rguilmet/magnetic-field-scanner/docs/electrical/wiring/RM3100 Breakout Board augumented pinout.png

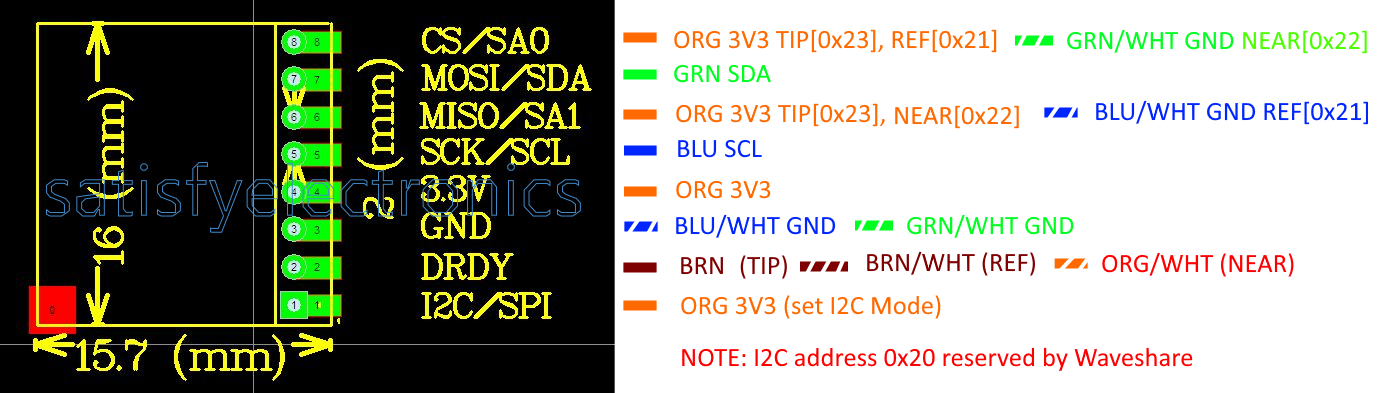
docs/electrical/wiring/RM3100 Breakout Board augumented pinout.png
