rguilmet/magnetic-field-scanner/docs/images/ESP32-S3-Touch-LCD-3.49-ArduinoToolCfg-18487604f20ee06f9c543932301bdffe.png

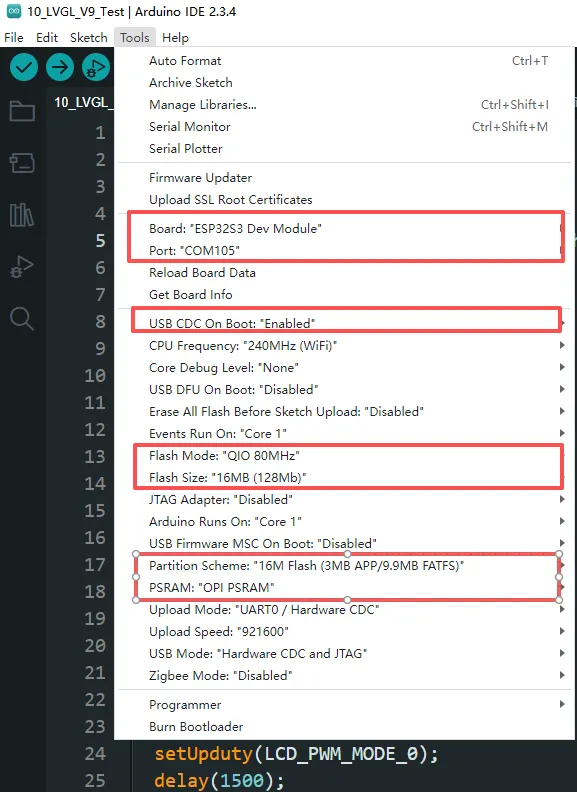
docs/images/ESP32-S3-Touch-LCD-3.49-ArduinoToolCfg-18487604f20ee06f9c543932301bdffe.png
