rguilmet/magnetic-field-scanner/docs/images/ESP32-S3-Touch-LCD-3.49-Blank_Portrait.png

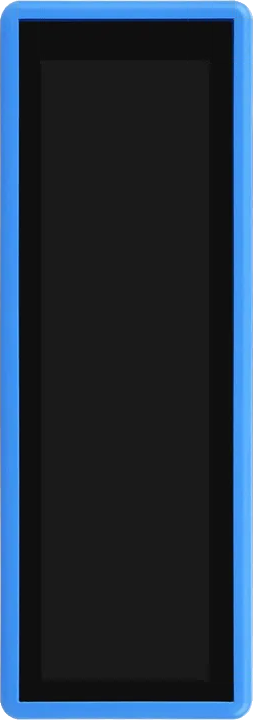
docs/images/ESP32-S3-Touch-LCD-3.49-Blank_Portrait.png
