rguilmet/magnetic-field-scanner/docs/images/ESP32-S3-Touch-LCD-3.49-DocHeader-1-2669fb1ab64cd743be19858549427792.png

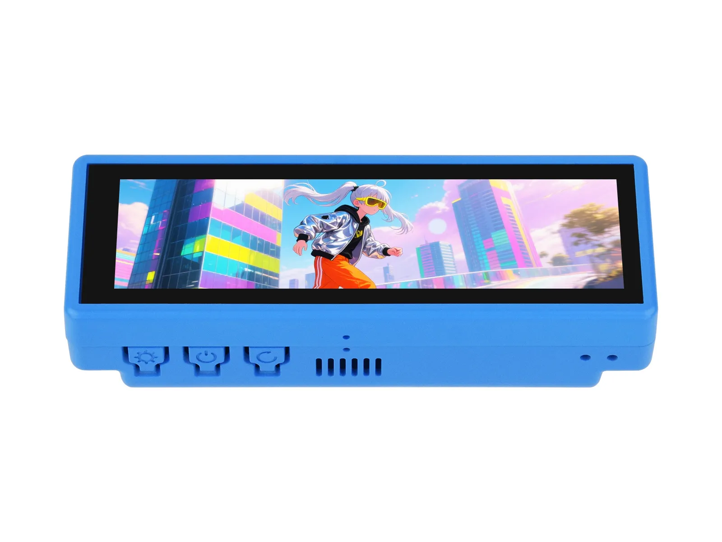
docs/images/ESP32-S3-Touch-LCD-3.49-DocHeader-1-2669fb1ab64cd743be19858549427792.png
