rguilmet/magnetic-field-scanner/docs/images/ESP32-S3-Touch-LCD-3.49-HW-d45f2a0617c5f4e05d497ae3533752b7.png

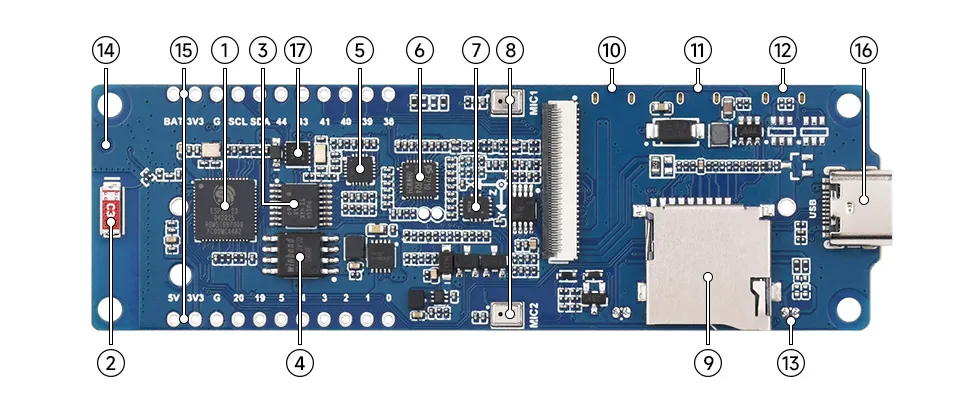
docs/images/ESP32-S3-Touch-LCD-3.49-HW-d45f2a0617c5f4e05d497ae3533752b7.png
