rguilmet/magnetic-field-scanner/docs/images/ESP32-S3-Touch-LCD-3.49-ProductSize-1-b798e9adb46e2dde7847e5227739baf6.png

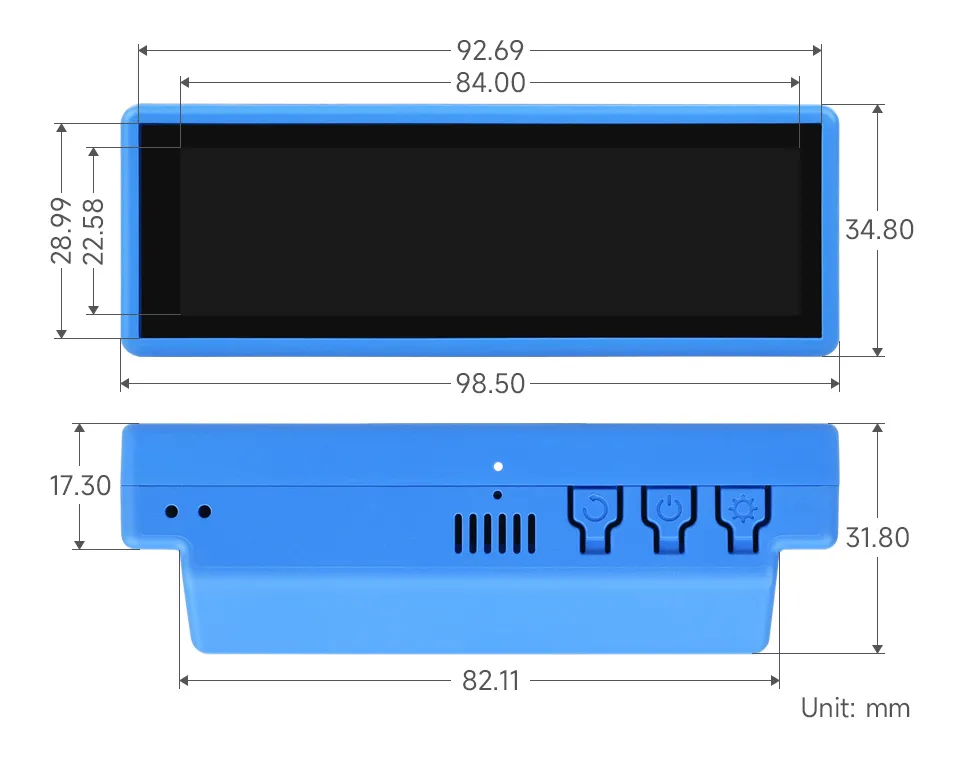
docs/images/ESP32-S3-Touch-LCD-3.49-ProductSize-1-b798e9adb46e2dde7847e5227739baf6.png
