rguilmet/magnetic-field-scanner/docs/images/ESP32-S3-Touch-LCD-3.49-ProductSize-2-53f7565186c1f234cee2f71812a7628d.png

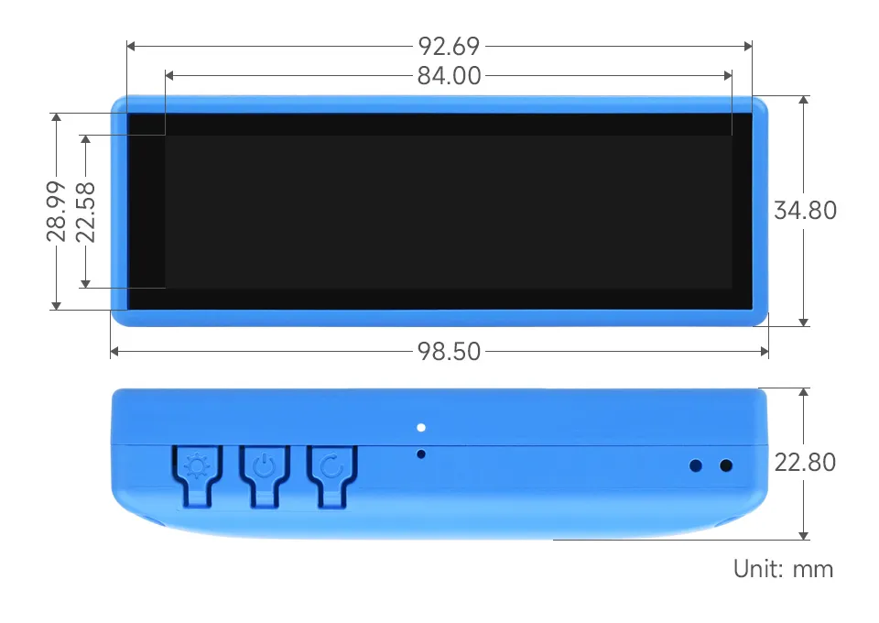
docs/images/ESP32-S3-Touch-LCD-3.49-ProductSize-2-53f7565186c1f234cee2f71812a7628d.png
