rguilmet/magnetic-field-scanner/docs/images/full_res/Magnetic Field Scanner - Exploded View - Closeup REF BACK (20260914_163832).png

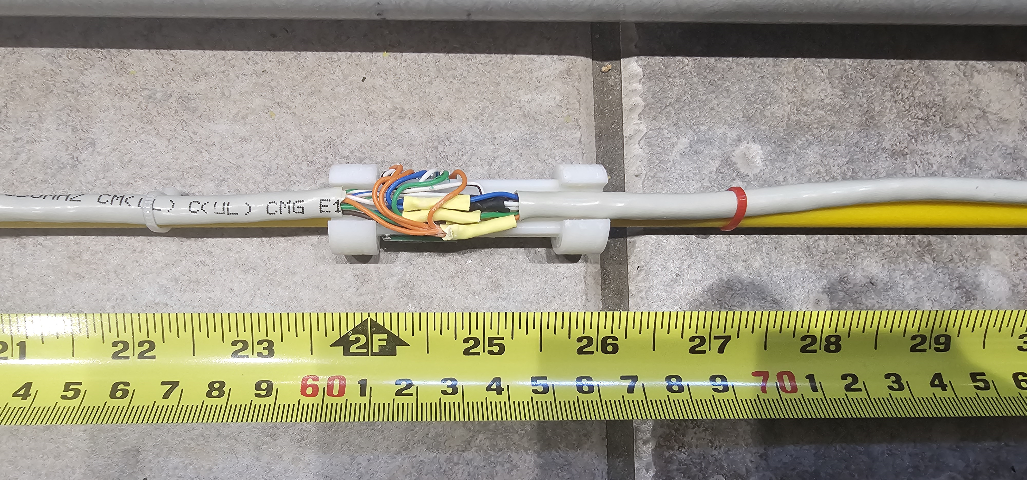
docs/images/full_res/Magnetic Field Scanner - Exploded View - Closeup REF BACK (20260914_163832).png
