rguilmet/magnetic-field-scanner/docs/images/full_res/Magnetic Field Scanner - Exploded View - Closeup TIP BACK (20260914_163811).png

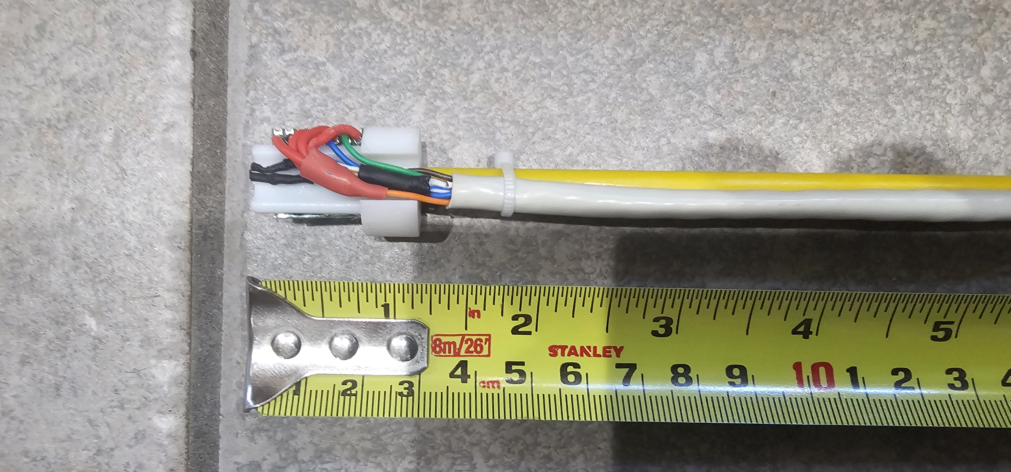
docs/images/full_res/Magnetic Field Scanner - Exploded View - Closeup TIP BACK (20260914_163811).png
