rguilmet/magnetic-field-scanner/docs/images/full_res/Magnetic Field Scanner - Inside Shot Overview (20260914_160351).png

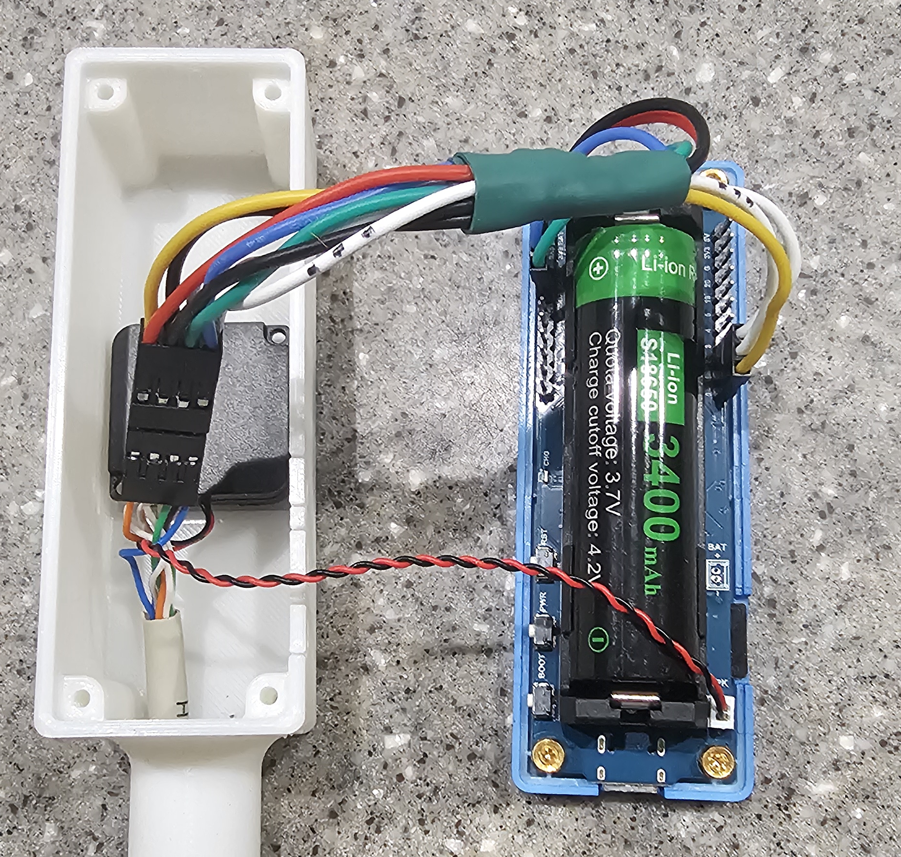
docs/images/full_res/Magnetic Field Scanner - Inside Shot Overview (20260914_160351).png
