rguilmet/magnetic-field-scanner/docs/images/Magnetic Field Scanner - Main Screen - AUTO.png

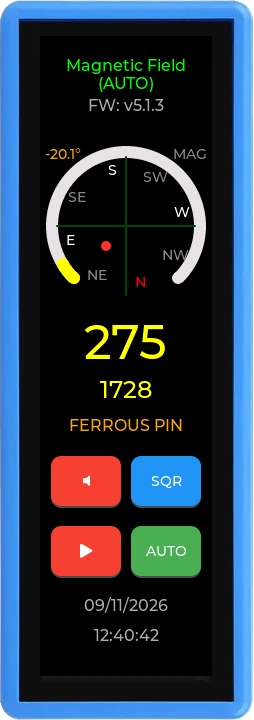
docs/images/Magnetic Field Scanner - Main Screen - AUTO.png
