rguilmet/magnetic-field-scanner/docs/images/Magnetic Field Scanner - Main Screen - RAW.png

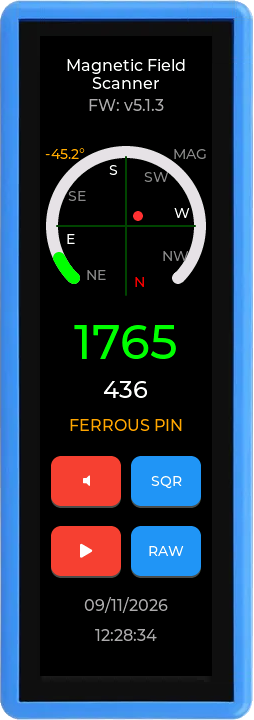
docs/images/Magnetic Field Scanner - Main Screen - RAW.png
