rguilmet/magnetic-field-scanner/docs/images/Magnetic Field Scanner - Mechanical Overview - 3 Sensor.png

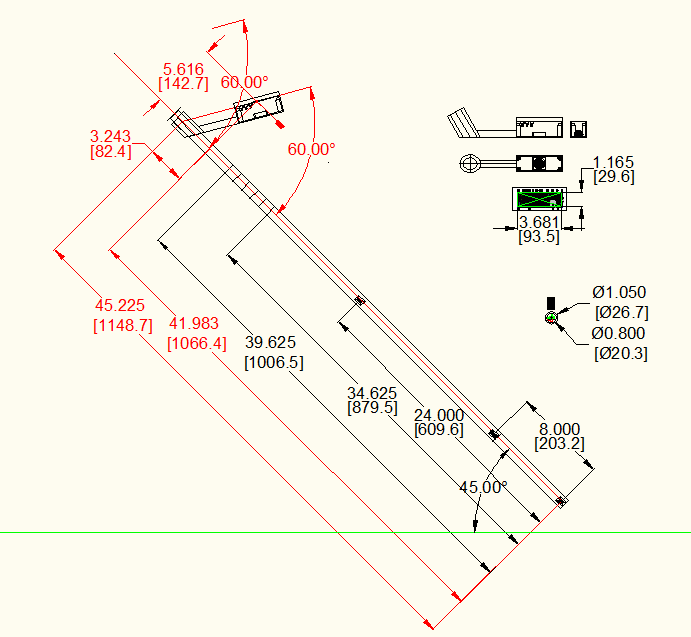
docs/images/Magnetic Field Scanner - Mechanical Overview - 3 Sensor.png
