rguilmet/magnetic-field-scanner/docs/images/Magnetic Field Scanner - Mechanical Overview.png

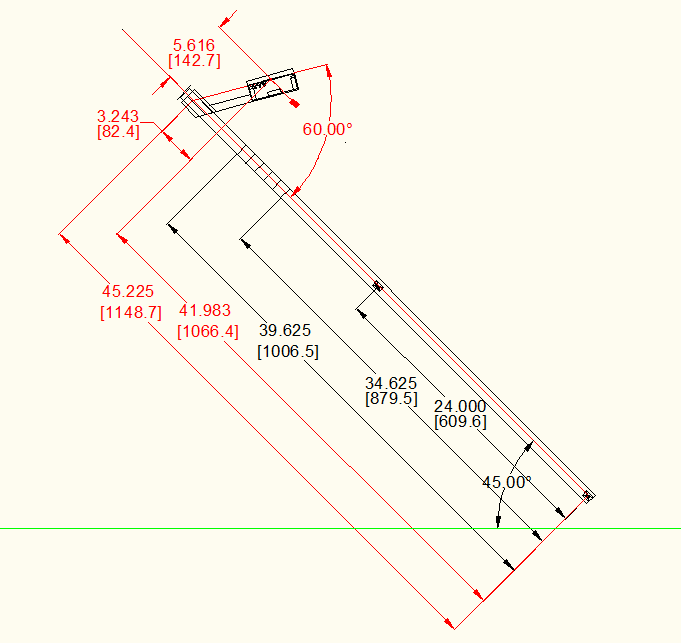
docs/images/Magnetic Field Scanner - Mechanical Overview.png
