rguilmet/magnetic-field-scanner/docs/images/Magnetic Field Scanner - System & Hardware - 200 CC.png

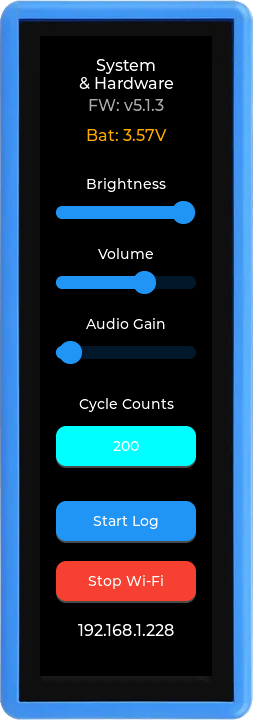
docs/images/Magnetic Field Scanner - System & Hardware - 200 CC.png
