rguilmet/magnetic-field-scanner/docs/reports/plot_45_45_400CC.png

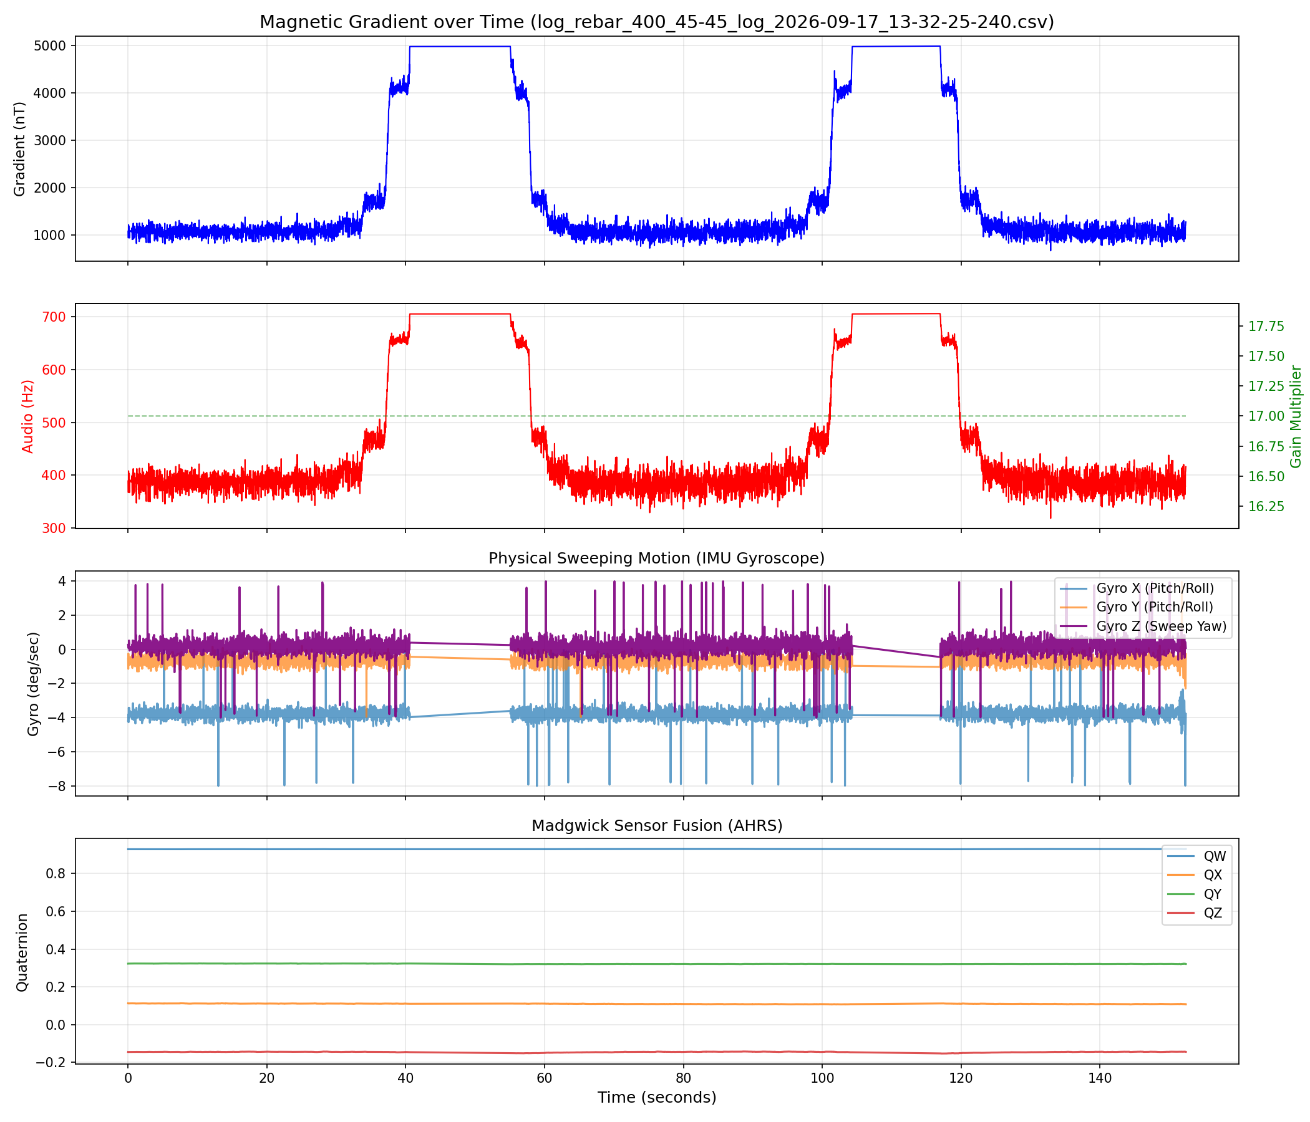
docs/reports/plot_45_45_400CC.png
