rguilmet/magnetic-field-scanner/docs/reports/plot_45_45_3200CC.png

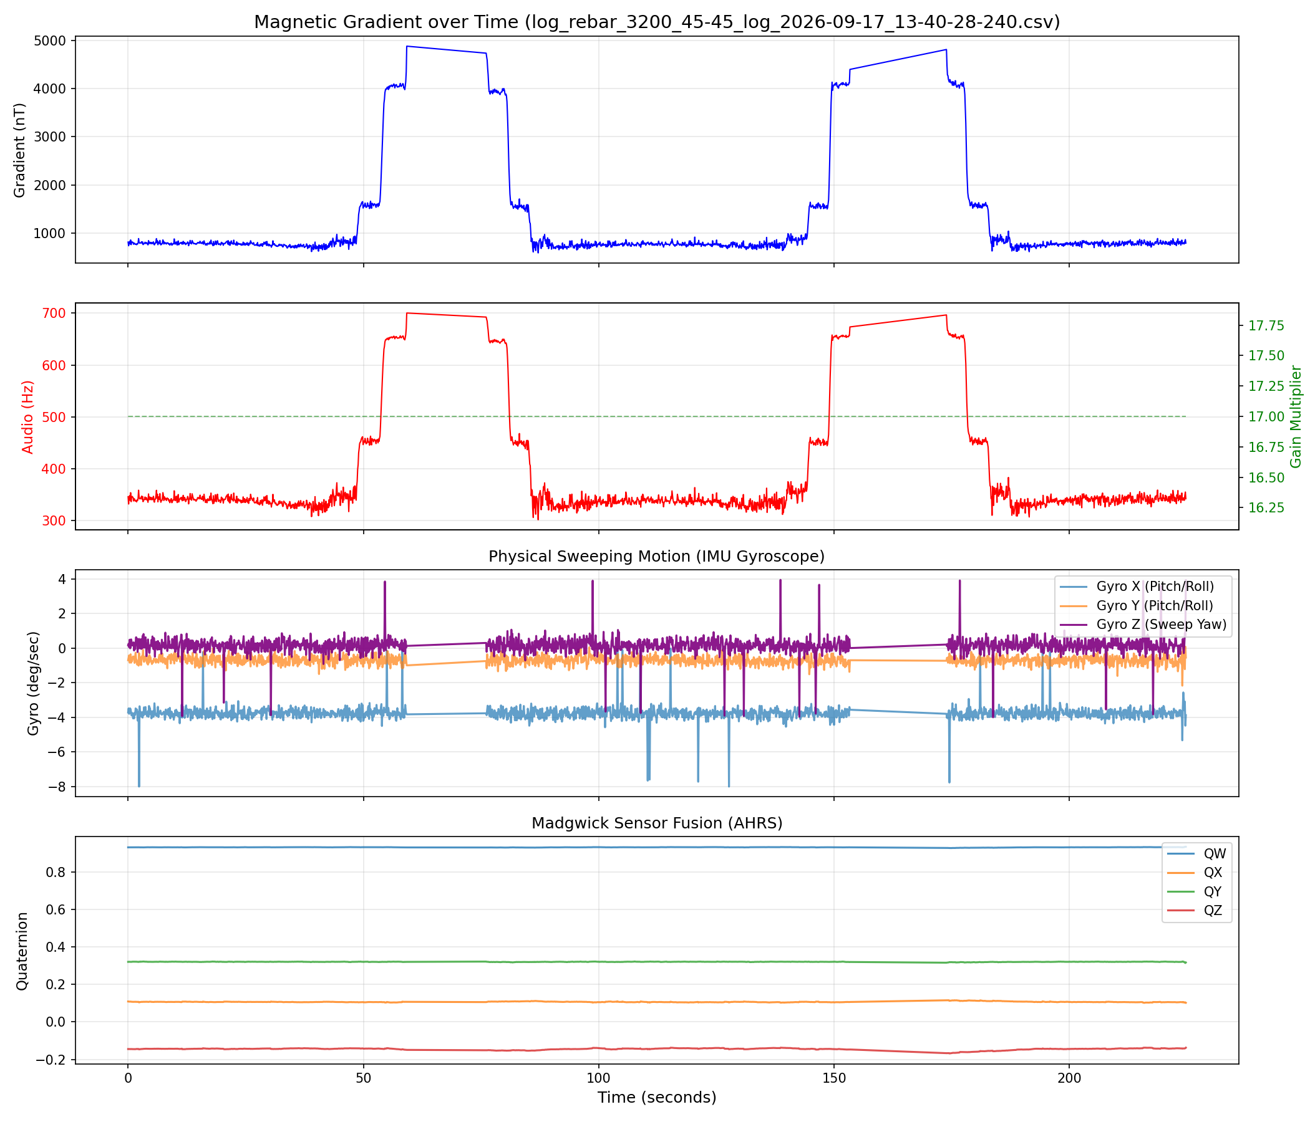
docs/reports/plot_45_45_3200CC.png
