rguilmet/magnetic-field-scanner/docs/reports/real_pin_sweep_800.png

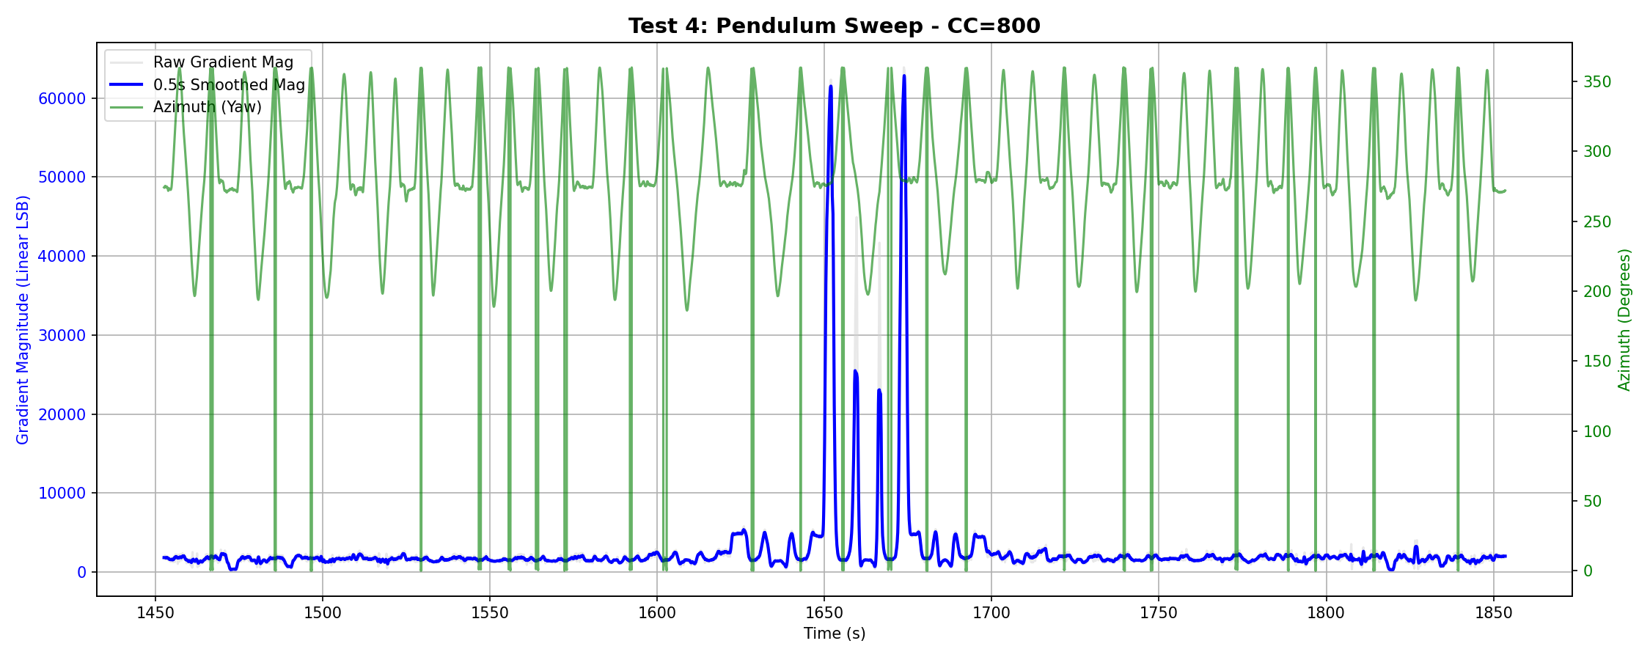
docs/reports/real_pin_sweep_800.png
