rguilmet/magnetic-field-scanner/docs/electrical/wiring/rm3100.png

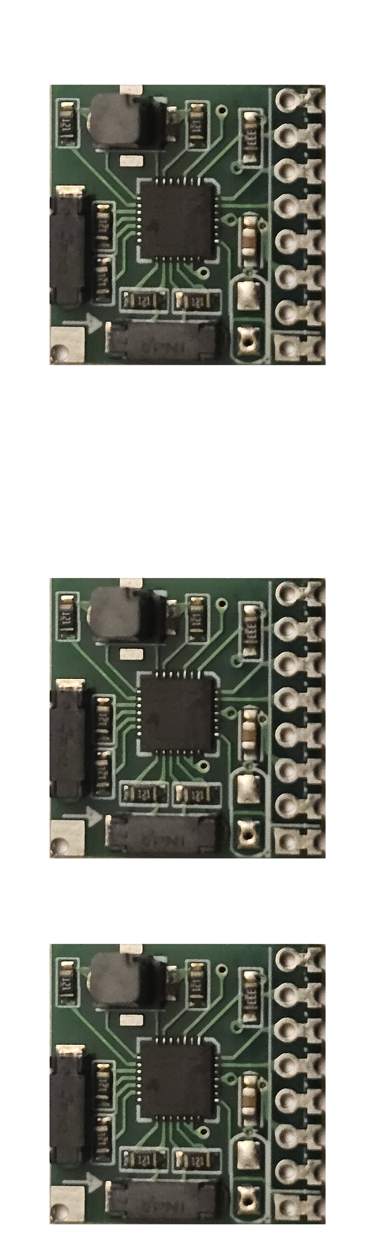
docs/electrical/wiring/rm3100.png
