rguilmet/magnetic-field-scanner/docs/images/full_res/Magnetic Field Scanner - Exploded View - Closeup Wand Wiring (20260914_164039).png

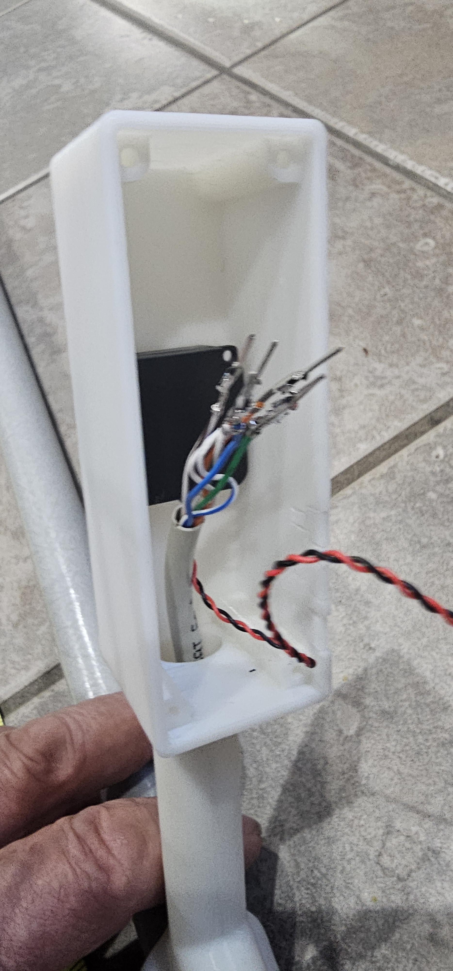
docs/images/full_res/Magnetic Field Scanner - Exploded View - Closeup Wand Wiring (20260914_164039).png
