rguilmet/magnetic-field-scanner/docs/images/full_res/Magnetic Field Scanner - Exploded View - Reassembly REF (20260914_163912).png

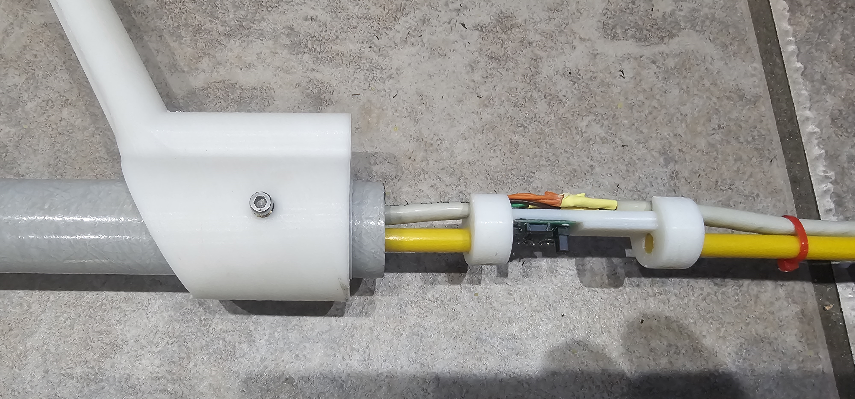
docs/images/full_res/Magnetic Field Scanner - Exploded View - Reassembly REF (20260914_163912).png
