rguilmet/magnetic-field-scanner/docs/reports/rebar_steps.png

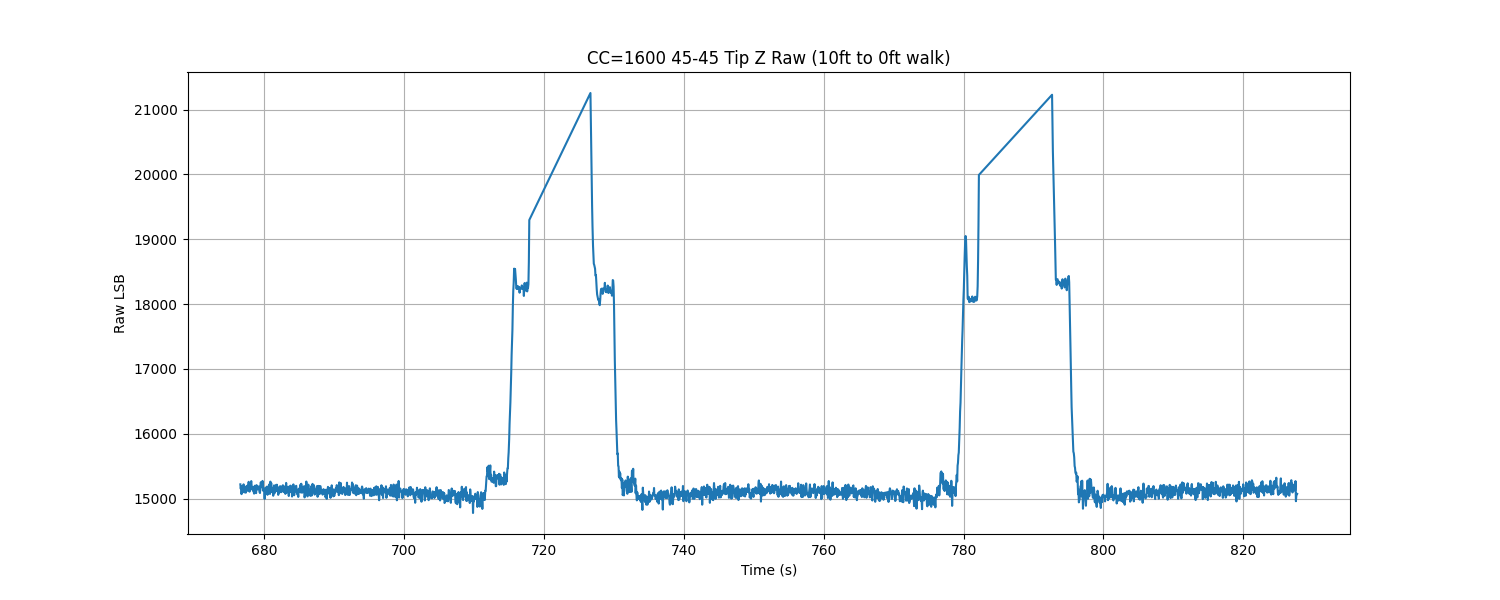
docs/reports/rebar_steps.png
