rguilmet/magnetic-field-scanner/characterization/Saturation Data Detail on Sensor Core Saturation.xlsx

t_200 | mag_200 | t_400 | mag_400 | t_800 | mag_800 | t_1600 | mag_1600 | t_3200 | mag_3200 | t | mag_200 | mag_400 | mag_800 | mag_1600 | mag_3200
0 | 2512.22 | 0 | 904.750 | 0 | 1285.46 | 0 | 1010.70 | 0 | 967.310 | 0 | 2512.22 | 904.75 | 1285.46 | 1010.7 | 967.31
34 | 2434.04 | 25 | 1015.510 | 34 | 1240.69 | 62 | 888.67 | 108 | 1003.530 | 25 | #N/A | 1015.51 | #N/A | #N/A | #N/A
56 | 2272.27 | 47 | 968.960 | 65 | 1455.58 | 122 | 970.00 | 213 | 922.020 | 34 | 2434.04 | #N/A | 1240.69 | #N/A | #N/A
85 | 2126.76 | 69 | 1026.730 | 98 | 936.43 | 182 | 949.60 | 319 | 952.990 | 47 | #N/A | 968.96 | #N/A | #N/A | #N/A
116 | 2400.28 | 90 | 974.590 | 133 | 1139.42 | 266 | 1017.67 | 424 | 962.720 | 56 | 2272.27 | #N/A | #N/A | #N/A | #N/A
140 | 2390.3 | 115 | 971.100 | 170 | 927.72 | 356 | 1044.16 | 530 | 959.580 | 62 | #N/A | #N/A | #N/A | 888.67 | #N/A
175 | 2377.63 | 136 | 960.070 | 203 | 1017.49 | 433 | 993.92 | 635 | 953.450 | 65 | #N/A | #N/A | 1455.58 | #N/A | #N/A
201 | 2574.69 | 155 | 968.220 | 239 | 925.82 | 528 | 1007.58 | 741 | 947.060 | 69 | #N/A | 1026.73 | #N/A | #N/A | #N/A
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
