rguilmet/magnetic-field-scanner/characterization/log_rebar_3200_log_2026-09-11_09-12-26-240-17uT.csv

time_ms | timestamp | version | voltage | audio_gain | cc | refX_raw | refY_raw | refZ_raw | tipX_raw | tipY_raw | tipZ_raw | refX_cal | refY_cal | refZ_cal | tipX_cal | tipY_cal | tipZ_cal | calOffsetX | calOffsetY | calOffsetZ | gradX | gradY | gradZ | mag | nT | accX | accY | accZ | gyrX | gyrY | gyrZ | imu_temp | freq | is_muted | QW | QX | QY | QZ | Azimuth | Elevation | Declination
2928953 | 2026-09-11_09-12-26.953-240 | v5.1.3 | 3.43 | 12.0 | 3200 | 17744 | 20155 | 56325 | 9619 | 17803 | 59113 | 14469.76 | 15456.15 | 45732.51 | 15473.66 | 15729.38 | 45909.04 | 0.00 | 0.00 | 0.00 | 1003.89 | 273.22 | 176.54 | 1055.28 | 1055.28 | 0.989 | 0.045 | 0.556 | -4.609 | -0.734 | 0.516 | 10822 | 172.1 | 0 | -0.9489 | -0.0229 | 0.0029 | -0.3147 | 36.7 | -1.1 | 0.0
2929062 | 2026-09-11_09-12-27.063-240 | v5.1.3 | 3.43 | 12.0 | 3200 | 17795 | 20236 | 56336 | 9655 | 17906 | 59099 | 14511.40 | 15522.32 | 45740.78 | 15498.62 | 15813.55 | 45891.59 | 0.00 | 0.00 | 0.00 | 987.22 | 291.23 | 150.81 | 1040.27 | 1040.27 | 1.004 | 0.057 | 0.548 | -3.391 | -0.969 | 0.078 | 10822 | 170.2 | 0 | -0.9485 | -0.0271 | 0.0034 | -0.3157 | 36.8 | -1.4 | 0.0
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
