rguilmet/magnetic-field-scanner/characterization/v5.1.3 & v5.1.4/log_rebar_200_log_2026-09-11_09-07-27-240.xlsx

time_ms | timestamp | version | voltage | audio_gain | cc | refX_raw | refY_raw | refZ_raw | tipX_raw | tipY_raw | tipZ_raw | refX_cal | refY_cal | refZ_cal | tipX_cal | tipY_cal | tipZ_cal | calOffsetX | calOffsetY | calOffsetZ | gradX | gradY | gradZ | mag | nT | accX | accY | accZ | gyrX | gyrY | gyrZ | imu_temp | freq | is_muted | QW | QX | QY | QZ | Azimuth | Elevation | Declination
2629828 | 2026-09-11_09-07-27.828-240 | v5.1.3 | 3.44 | 12 | 200 | 1139 | 1260 | 3510 | 623 | 1080 | 3686 | 14866.65 | 15458.44 | 45598.09 | 15755.92 | 15303.56 | 45757.91 | 0 | 0 | 0 | 889.26 | -154.87 | 159.82 | 916.69 | 916.69 | 1.015 | 0.103 | 0.518 | -3.453 | -0.812 | -0.469 | 10359 | 154.4 | 0 | -0.9499 | -0.0314 | 0.0055 | -0.311 | 36.2 | -1.7 | 0
2629862 | 2026-09-11_09-07-27.863-240 | v5.1.3 | 3.44 | 12 | 200 | 1144 | 1257 | 3508 | 641 | 1088 | 3680 | 14933.13 | 15418.58 | 45572.45 | 15976.33 | 15409.3 | 45639.86 | 0 | 0 | 0 | 1043.2 | -9.28 | 67.41 | 1045.42 | 1045.42 | 1.005 | 0.032 | 0.544 | -5.266 | -0.469 | 0.391 | 10359 | 170.8 | 0 | -0.9499 | -0.0313 | 0.0057 | -0.3108 | 36.2 | -1.7 | 0
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
