rguilmet/magnetic-field-scanner/characterization/v3.6.27/cal_1_calibration_2026-08-29_17-11-49-240.csv

time_ms | timestamp | version | voltage | audio_gain | cc | refX_raw | refY_raw | refZ_raw | tipX_raw | tipY_raw | tipZ_raw | refX_cal | refY_cal | refZ_cal | tipX_cal | tipY_cal | tipZ_cal | calOffsetX | calOffsetY | calOffsetZ | gradX | gradY | gradZ | mag | nT | accX | accY | accZ | gyrX | gyrY | gyrZ | freq | is_muted | QW | QX | QY | QZ | Azimuth | Elevation | Declination
245933 | 2026-08-29_17-11-49.935-240 | v3.6.25 | 3.52 | 12.0 | 400 | 1907 | 360 | 7479 | 663 | 243 | 7764 | 1804 | 242 | 7479 | 1756 | 70 | 7535 | 0 | 0 | 0 | -48 | -172 | 56 | 187.1 | 1231.2 | 0.679 | 0.013 | 0.847 | -5.844 | -1.875 | 5.391 | 194.5 | 0 | -0.3810 | 0.1701 | -0.0666 | -0.9064 | 134.3 | 21.0 | 0.0
245977 | 2026-08-29_17-11-49.978-240 | v3.6.25 | 3.52 | 12.0 | 400 | 1907 | 360 | 7479 | 638 | 231 | 7775 | 1804 | 242 | 7479 | 1733 | 58 | 7550 | 0 | 0 | 0 | -71 | -184 | 71 | 209.6 | 1379.0 | 0.689 | -0.006 | 0.831 | -3.953 | 0.438 | -0.828 | 213.4 | 0 | -0.3810 | 0.1697 | -0.0660 | -0.9064 | 134.3 | 21.0 | 0.0
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
