rguilmet/magnetic-field-scanner/characterization/v3.6.27/cal_2_calibration_2026-08-30_09-19-37-240.csv

time_ms | timestamp | version | voltage | audio_gain | cc | refX_raw | refY_raw | refZ_raw | tipX_raw | tipY_raw | tipZ_raw | refX_cal | refY_cal | refZ_cal | tipX_cal | tipY_cal | tipZ_cal | calOffsetX | calOffsetY | calOffsetZ | gradX | gradY | gradZ | mag | nT | accX | accY | accZ | gyrX | gyrY | gyrZ | freq | is_muted | QW | QX | QY | QZ | Azimuth | Elevation | Declination
633638 | 2026-08-30_09-19-37.640-240 | v3.6.25 | 3.47 | 12.0 | 400 | -18 | 5811 | 5159 | -725 | 5903 | 5129 | -177 | 5741 | 5104 | -221 | 5609 | 5176 | 0 | 0 | 0 | -44 | -132 | 72 | 156.7 | 1030.7 | 0.654 | -0.018 | 0.879 | 4.031 | -2.281 | -10.000 | 168.9 | 1 | 0.9312 | 0.2286 | -0.2449 | -0.1434 | 335.7 | -23.0 | 0.0
633691 | 2026-08-30_09-19-37.692-240 | v3.6.25 | 3.47 | 12.0 | 400 | 24 | 5794 | 5175 | -725 | 5903 | 5129 | -134 | 5723 | 5120 | -221 | 5609 | 5176 | 0 | 0 | 0 | -87 | -114 | 56 | 154.0 | 1012.8 | 0.684 | -0.004 | 0.875 | 1.984 | -1.812 | -10.828 | 166.7 | 1 | 0.9309 | 0.2304 | -0.2447 | -0.1431 | 335.7 | -22.9 | 0.0
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
