rguilmet/magnetic-field-scanner/characterization/v3.6.27/cal_3_calibration_2026-08-30_09-24-25-240.csv

time_ms | timestamp | version | voltage | audio_gain | cc | refX_raw | refY_raw | refZ_raw | tipX_raw | tipY_raw | tipZ_raw | refX_cal | refY_cal | refZ_cal | tipX_cal | tipY_cal | tipZ_cal | calOffsetX | calOffsetY | calOffsetZ | gradX | gradY | gradZ | mag | nT | accX | accY | accZ | gyrX | gyrY | gyrZ | freq | is_muted | QW | QX | QY | QZ | Azimuth | Elevation | Declination
921765 | 2026-08-30_09-24-25.767-240 | v3.6.25 | 3.47 | 12.0 | 400 | 2637 | 865 | 7224 | 1408 | 745 | 7653 | 2582 | 695 | 7188 | 2598 | 685 | 7251 | 0 | 0 | 0 | 16 | -10 | 63 | 65.8 | 432.7 | 0.620 | 0.100 | 0.871 | 3.672 | -1.922 | -1.797 | 92.6 | 1 | -0.0782 | -0.2279 | 0.0200 | 0.9703 | 190.3 | 26.0 | 0.0
921816 | 2026-08-30_09-24-25.818-240 | v3.6.25 | 3.47 | 12.0 | 400 | 2632 | 858 | 7225 | 1408 | 745 | 7653 | 2577 | 688 | 7189 | 2598 | 685 | 7251 | 0 | 0 | 0 | 21 | -3 | 62 | 65.5 | 431.1 | 0.628 | 0.206 | 0.889 | 0.250 | -2.047 | 0.422 | 92.4 | 1 | -0.0787 | -0.2277 | 0.0215 | 0.9703 | 190.4 | 26.0 | 0.0
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
