rguilmet/magnetic-field-scanner/characterization/v3.6.27/cal_4_calibration_2026-08-30_09-29-53-240.csv

time_ms | timestamp | version | voltage | audio_gain | cc | refX_raw | refY_raw | refZ_raw | tipX_raw | tipY_raw | tipZ_raw | refX_cal | refY_cal | refZ_cal | tipX_cal | tipY_cal | tipZ_cal | calOffsetX | calOffsetY | calOffsetZ | gradX | gradY | gradZ | mag | nT | accX | accY | accZ | gyrX | gyrY | gyrZ | freq | is_muted | QW | QX | QY | QZ | Azimuth | Elevation | Declination
1250186 | 2026-08-30_09-29-54.188-240 | v3.6.25 | 3.46 | 12.0 | 400 | 4025 | 5220 | 4224 | 3349 | 5271 | 4873 | 3934 | 5125 | 4152 | 3973 | 5159 | 4193 | 0 | 0 | 0 | 39 | 34 | 41 | 66.0 | 434.3 | 0.311 | 0.147 | 1.018 | -1.953 | -1.016 | -2.516 | 92.9 | 1 | -0.6062 | -0.7104 | 0.3053 | -0.1861 | 344.4 | -39.4 | 0.0
1250236 | 2026-08-30_09-29-54.238-240 | v3.6.25 | 3.46 | 12.0 | 400 | 4040 | 5202 | 4191 | 3402 | 5263 | 4861 | 3950 | 5107 | 4119 | 4024 | 5151 | 4172 | 0 | 0 | 0 | 74 | 44 | 53 | 101.1 | 665.1 | 0.303 | 0.124 | 0.993 | -4.250 | -0.250 | 1.000 | 122.3 | 1 | -0.6066 | -0.7102 | 0.3051 | -0.1859 | 344.4 | -39.4 | 0.0
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
