rguilmet/magnetic-field-scanner/characterization/v3.6.27/cal_5_calibration_2026-08-30_16-02-45-240.csv

time_ms | timestamp | version | voltage | audio_gain | cc | refX_raw | refY_raw | refZ_raw | tipX_raw | tipY_raw | tipZ_raw | refX_cal | refY_cal | refZ_cal | tipX_cal | tipY_cal | tipZ_cal | calOffsetX | calOffsetY | calOffsetZ | gradX | gradY | gradZ | mag | nT | accX | accY | accZ | gyrX | gyrY | gyrZ | freq | is_muted | QW | QX | QY | QZ | Azimuth | Elevation | Declination
18008 | 2026-08-30_16-02-45.009-240 | v3.6.25 | 3.48 | 12.0 | 400 | -1859 | 2226 | 7127 | -2961 | 2244 | 6875 | -2005 | 2148 | 7107 | -2072 | 1984 | 7251 | 0 | 0 | 0 | -67 | -164 | 144 | 228.3 | 1502.0 | 0.469 | -0.117 | 0.948 | -5.516 | 0.344 | -1.969 | 229.0 | 0 | 0.9721 | -0.0899 | 0.2137 | 0.0354 | 1.9 | 24.9 | 0.0
18058 | 2026-08-30_16-02-45.061-240 | v3.6.25 | 3.48 | 12.0 | 400 | -1859 | 2226 | 7127 | -3006 | 2275 | 6812 | -2005 | 2148 | 7107 | -2128 | 2013 | 7197 | 0 | 0 | 0 | -123 | -135 | 90 | 203.6 | 1339.5 | 0.454 | -0.126 | 0.952 | -2.703 | 0.547 | -6.203 | 208.3 | 0 | 0.9721 | -0.0896 | 0.2139 | 0.0344 | 1.8 | 25.0 | 0.0
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
