rguilmet/magnetic-field-scanner/characterization/v3.6.27/log_ahrs_2026-08-30_09-12-01-240.csv

time_ms | timestamp | version | voltage | audio_gain | cc | refX_raw | refY_raw | refZ_raw | tipX_raw | tipY_raw | tipZ_raw | refX_cal | refY_cal | refZ_cal | tipX_cal | tipY_cal | tipZ_cal | calOffsetX | calOffsetY | calOffsetZ | gradX | gradY | gradZ | mag | nT | accX | accY | accZ | gyrX | gyrY | gyrZ | freq | is_muted | QW | QX | QY | QZ | Azimuth | Elevation | Declination
178106 | 2026-08-30_09-12-02.108-240 | v3.6.25 | 3.48 | 12.0 | 400 | 1340 | 4895 | 5943 | 419 | 4920 | 6124 | 1193 | 4790 | 5894 | 1115 | 4655 | 5956 | 0 | 0 | 0 | -78 | -135 | 62 | 167.8 | 1103.9 | 0.752 | 0.119 | 0.802 | -3.312 | -1.422 | -1.625 | 178.3 | 1 | 0.9556 | 0.2540 | 0.1008 | 0.1104 | 15.4 | 7.8 | 0.0
178144 | 2026-08-30_09-12-02.146-240 | v3.6.25 | 3.48 | 12.0 | 400 | 1331 | 4899 | 5936 | 419 | 4920 | 6124 | 1183 | 4794 | 5887 | 1115 | 4655 | 5956 | 0 | 0 | 0 | -68 | -139 | 69 | 169.4 | 1114.7 | 0.781 | 0.189 | 0.793 | -3.719 | -2.250 | -0.375 | 179.6 | 1 | 0.9558 | 0.2533 | 0.1006 | 0.1101 | 15.3 | 7.8 | 0.0
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
