rguilmet/magnetic-field-scanner/characterization/v5.1.2/drift_analysis.png

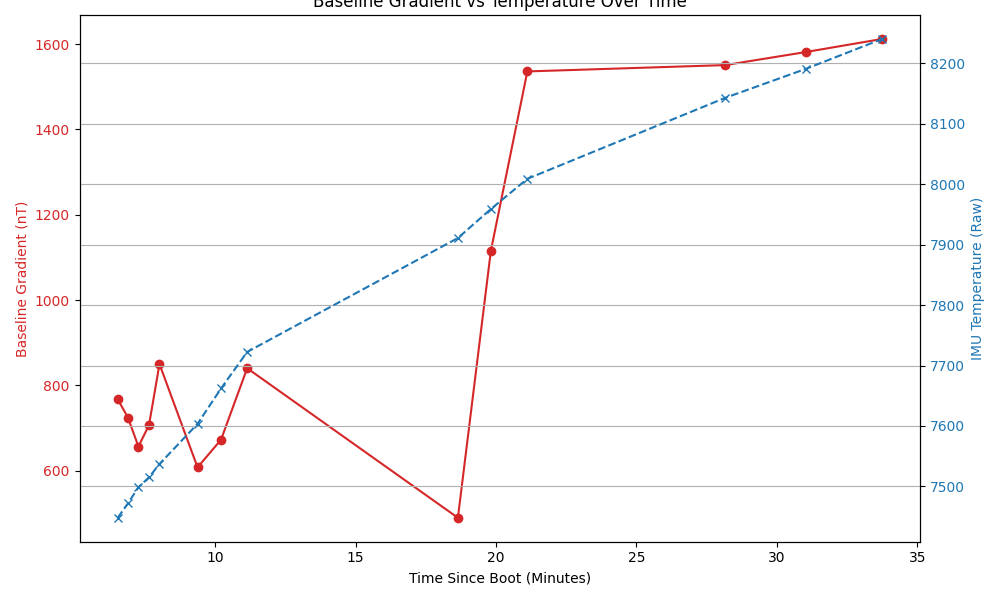
characterization/v5.1.2/drift_analysis.png
