rguilmet/magnetic-field-scanner/characterization/v5.1.3 & v5.1.4/rebar_3200_plot.png

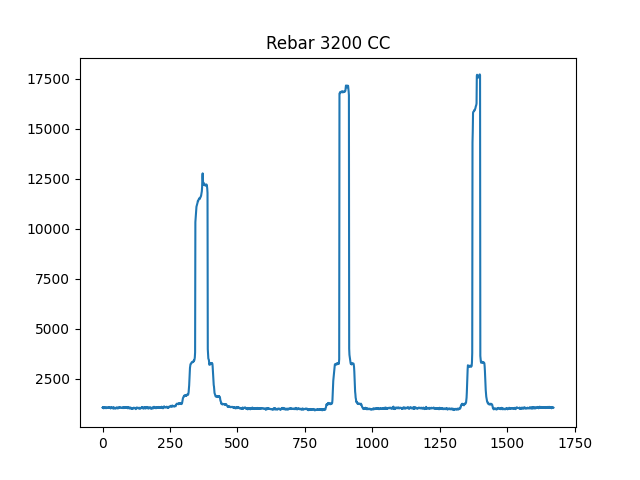
characterization/v5.1.3 & v5.1.4/rebar_3200_plot.png
