rguilmet/magnetic-field-scanner/docs/images/calibration/mag_cal_3d.png

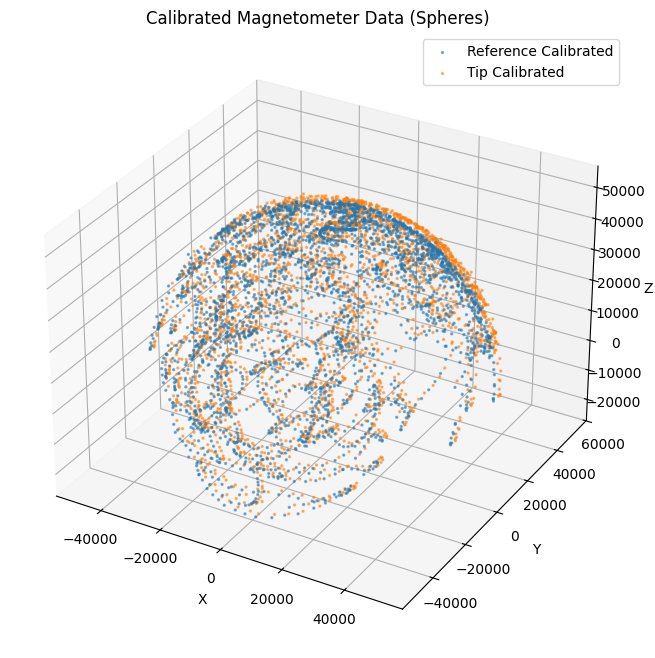
docs/images/calibration/mag_cal_3d.png
