rguilmet/magnetic-field-scanner/docs/images/Characterization Rebar using Wand at 45, 45 - Rear (20260917_132619.png

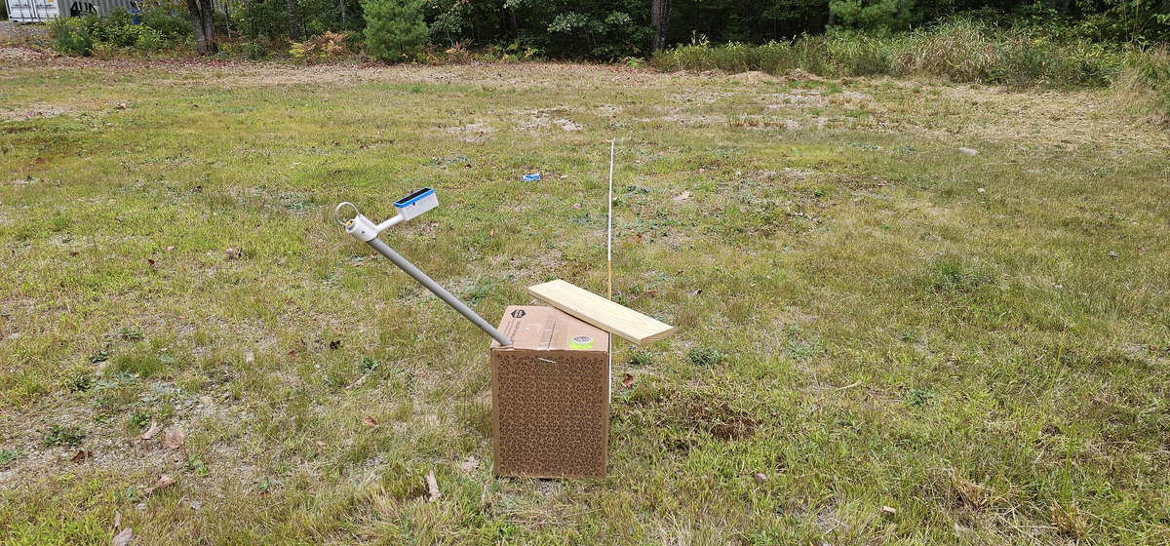
docs/images/Characterization Rebar using Wand at 45, 45 - Rear (20260917_132619.png
