rguilmet/magnetic-field-scanner/docs/articles/RM3100/RM3100 Magnetometer on a Chip.pdf

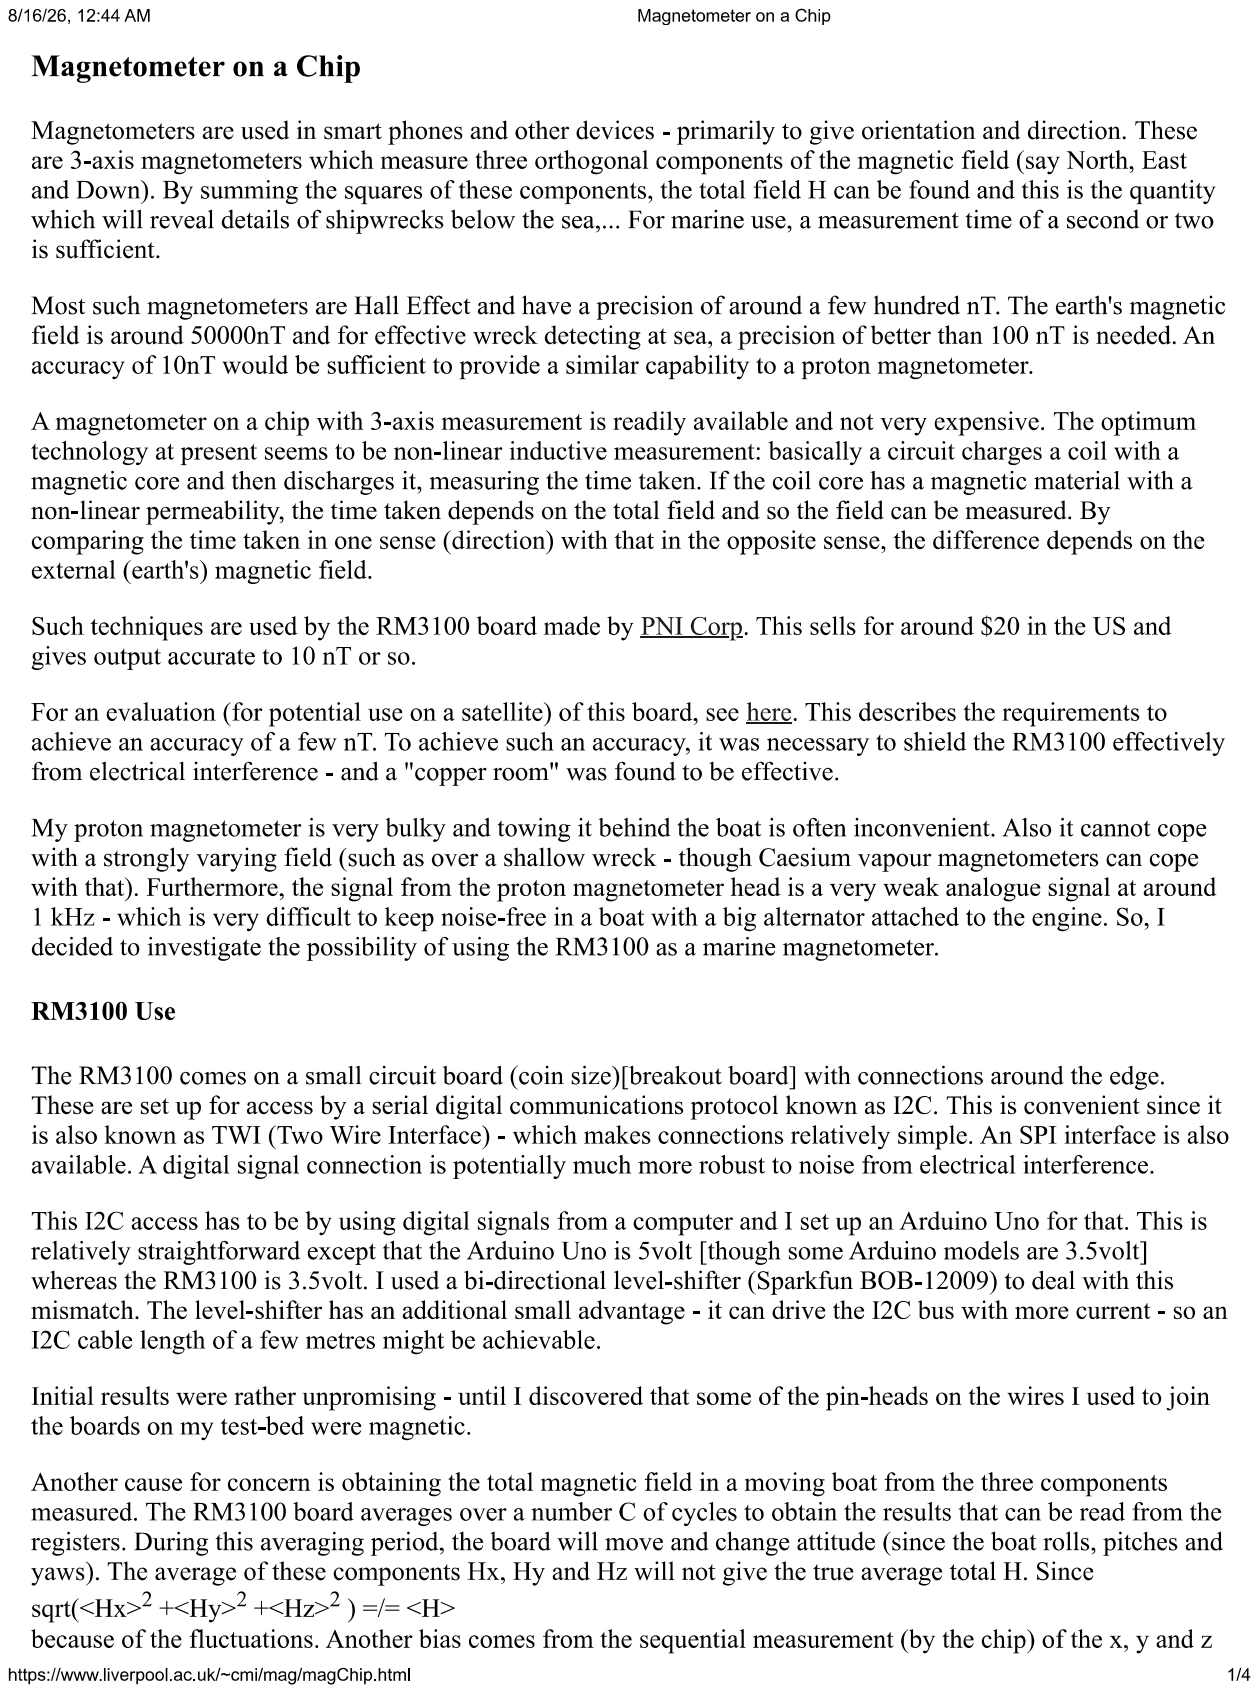
[picture p95: page 1]

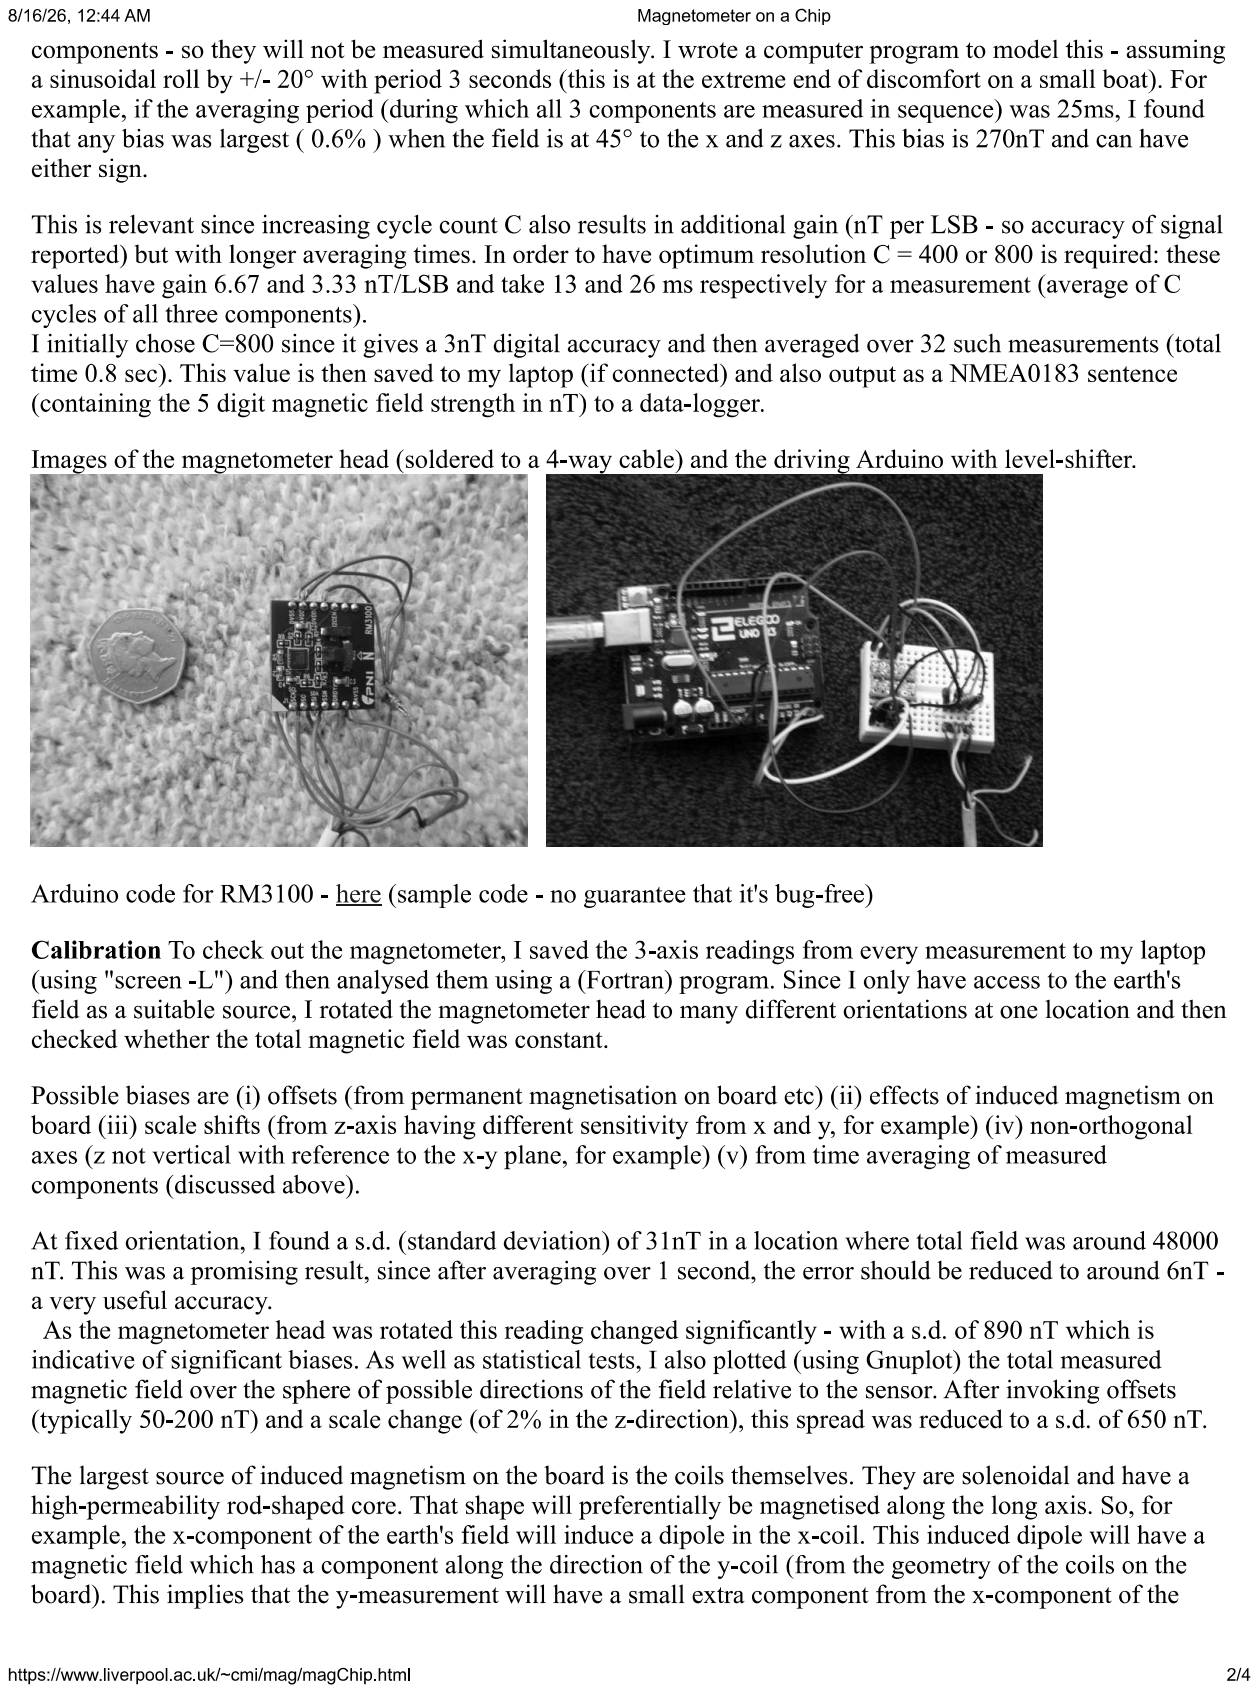
[picture p96: page 2]

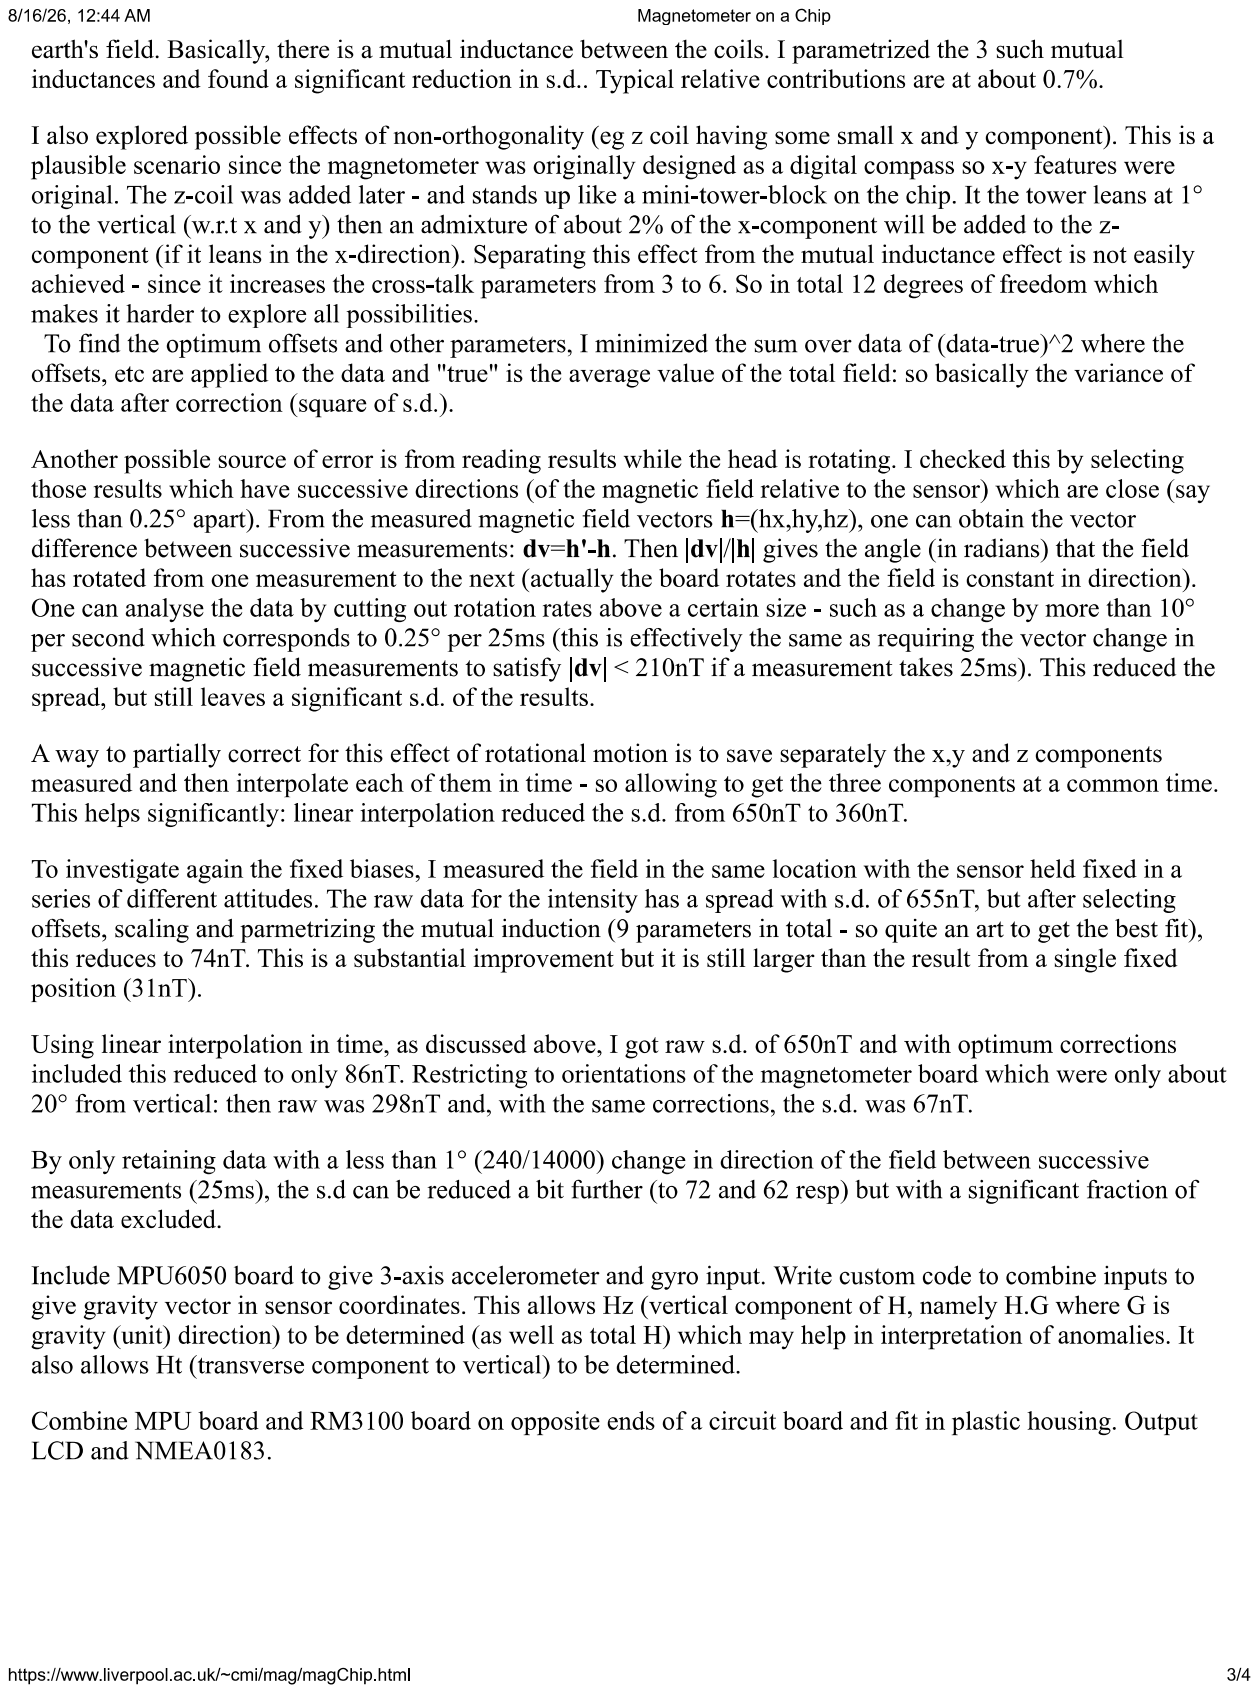
[picture p97: page 3]

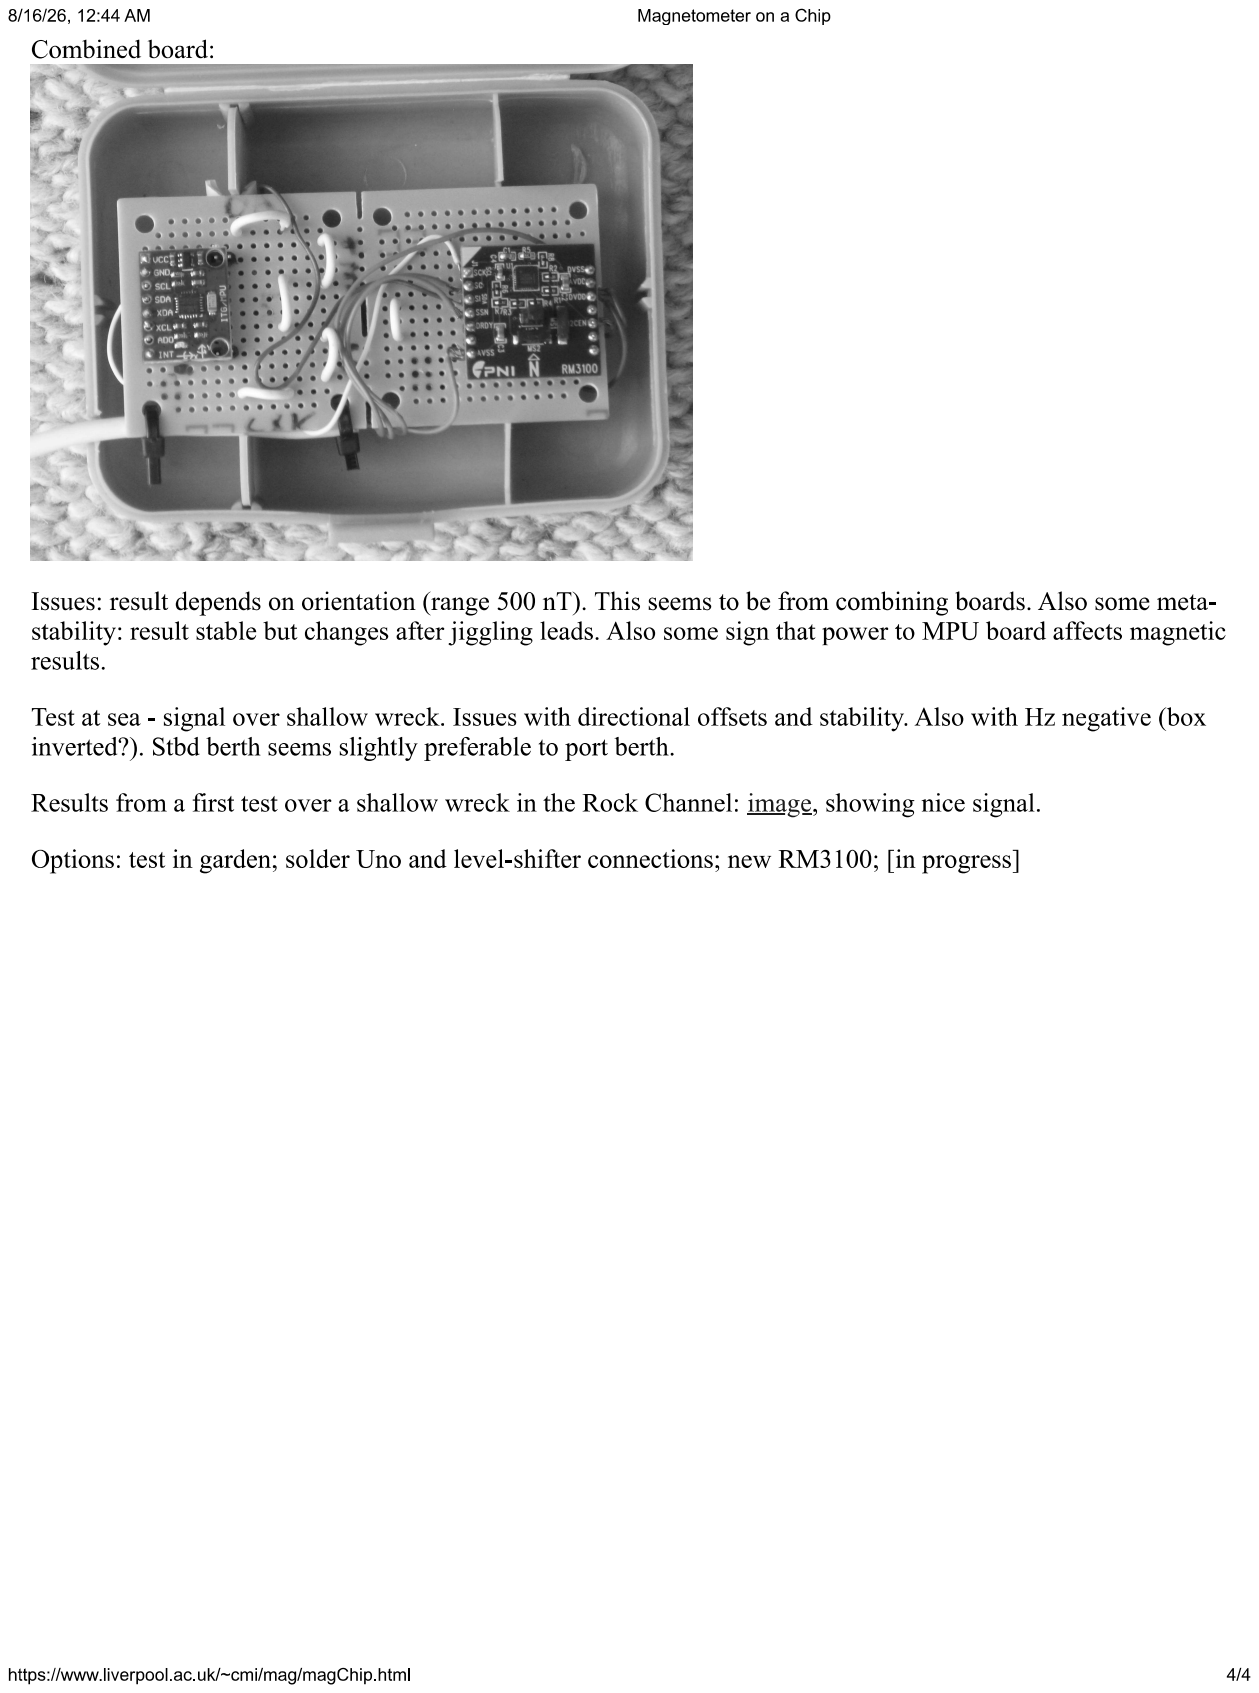
[picture p98: page 4]
