rguilmet/magnetic-field-scanner/src/i2c_bsp/i2c_bsp.c

#include <stdio.h>
#include "i2c_bsp.h"
#include "../../user_config.h"
#include "freertos/FreeRTOS.h"

i2c_master_bus_handle_t user_i2c_port0_handle = NULL;
i2c_master_bus_handle_t user_i2c_port1_handle = NULL;
i2c_master_dev_handle_t disp_touch_dev_handle = NULL;
i2c_master_dev_handle_t rtc_dev_handle = NULL;
i2c_master_dev_handle_t imu_dev_handle = NULL;


static uint32_t i2c_data_pdMS_TICKS = 0;
static uint32_t i2c_done_pdMS_TICKS = 0;


void i2c_master_Init(void)
{
  i2c_data_pdMS_TICKS = pdMS_TO_TICKS(50);
  i2c_done_pdMS_TICKS = pdMS_TO_TICKS(50);
  /*i2c_port 0 init*/
  i2c_master_bus_config_t i2c_bus_config = 
  {
    .clk_source = I2C_CLK_SRC_DEFAULT,
    .i2c_port = I2C_NUM_0,
    .scl_io_num = MFS_PIN_I2C0_SCL,
    .sda_io_num = MFS_PIN_I2C0_SDA,
    .glitch_ignore_cnt = 7,
    .flags = {
      .enable_internal_pullup = true,
    },
  };
  ESP_ERROR_CHECK(i2c_new_master_bus(&i2c_bus_config, &user_i2c_port0_handle));
  i2c_bus_config.scl_io_num = MFS_PIN_I2C1_TOUCH_SCL;
  i2c_bus_config.sda_io_num = MFS_PIN_I2C1_TOUCH_SDA;
  i2c_bus_config.i2c_port = I2C_NUM_1;
  ESP_ERROR_CHECK(i2c_new_master_bus(&i2c_bus_config, &user_i2c_port1_handle));
  
  i2c_device_config_t dev_cfg = 
  {
    .dev_addr_length = I2C_ADDR_BIT_LEN_7,
    .scl_speed_hz = 200000,
  };
  dev_cfg.device_address = MFS_RTC_ADDR;
  ESP_ERROR_CHECK(i2c_master_bus_add_device(user_i2c_port0_handle, &dev_cfg, &rtc_dev_handle));

  dev_cfg.device_address = MFS_IMU_ADDR;
  ESP_ERROR_CHECK(i2c_master_bus_add_device(user_i2c_port0_handle, &dev_cfg, &imu_dev_handle));

  dev_cfg.device_address = I2C_TOUCH_ADDR;
  ESP_ERROR_CHECK(i2c_master_bus_add_device(user_i2c_port1_handle, &dev_cfg, &disp_touch_dev_handle));

}

uint8_t i2c_write_buff(i2c_master_dev_handle_t dev_handle,int reg,uint8_t *buf,uint8_t len)
{
  uint8_t ret;
  ret = i2c_master_bus_wait_all_done(user_i2c_port0_handle,i2c_done_pdMS_TICKS);
  if(ret != ESP_OK)
  return ret;
  if(reg == -1)
  {
    ret = i2c_master_transmit(dev_handle,buf,len,i2c_data_pdMS_TICKS);
  }
  else
  {
    uint8_t pbuf[len+1];
    pbuf[0] = reg;
    for(uint8_t i = 0; i<len; i++)
    {
      pbuf[i+1] = buf[i];
    }
    ret = i2c_master_transmit(dev_handle,pbuf,len+1,i2c_data_pdMS_TICKS);
  }
  return ret;
}
uint8_t i2c_master_write_read_dev(i2c_master_dev_handle_t dev_handle,uint8_t *writeBuf,uint8_t writeLen,uint8_t *readBuf,uint8_t readLen)
{
  uint8_t ret;
  ret = i2c_master_bus_wait_all_done(user_i2c_port0_handle,i2c_done_pdMS_TICKS);
  if(ret != ESP_OK)
  return ret;
  ret = i2c_master_transmit_receive(dev_handle,writeBuf,writeLen,readBuf,readLen,i2c_data_pdMS_TICKS);
  return ret;
}
uint8_t i2c_read_buff(i2c_master_dev_handle_t dev_handle,int reg,uint8_t *buf,uint8_t len)
{
  uint8_t ret;
  uint8_t addr = 0;
  ret = i2c_master_bus_wait_all_done(user_i2c_port0_handle,i2c_done_pdMS_TICKS);
  if(ret != ESP_OK)
  return ret;
  if( reg == -1 )
  {ret = i2c_master_receive(dev_handle, buf,len, i2c_data_pdMS_TICKS);}
  else
  {addr = (uint8_t)reg; ret = i2c_master_transmit_receive(dev_handle,&addr,1,buf,len,i2c_data_pdMS_TICKS);}
  return ret;
}


uint8_t i2c_master_touch_write_read(i2c_master_dev_handle_t dev_handle,uint8_t *writeBuf,uint8_t writeLen,uint8_t *readBuf,uint8_t readLen)
{
  uint8_t ret;
  ret = i2c_master_bus_wait_all_done(user_i2c_port1_handle,i2c_done_pdMS_TICKS);
  if(ret != ESP_OK)
  return ret;
  ret = i2c_master_transmit_receive(dev_handle,writeBuf,writeLen,readBuf,readLen,i2c_data_pdMS_TICKS);
  return ret;
}
